DominionEng/CV-19_Guardian_Masks/Photos/(2).jpg

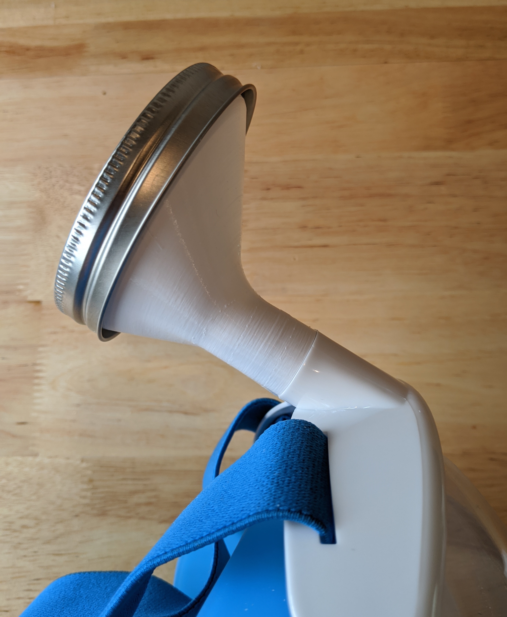
Photos/(2).jpg
