DominionEng/CV-19_Guardian_Masks/Photos/(3).jpg

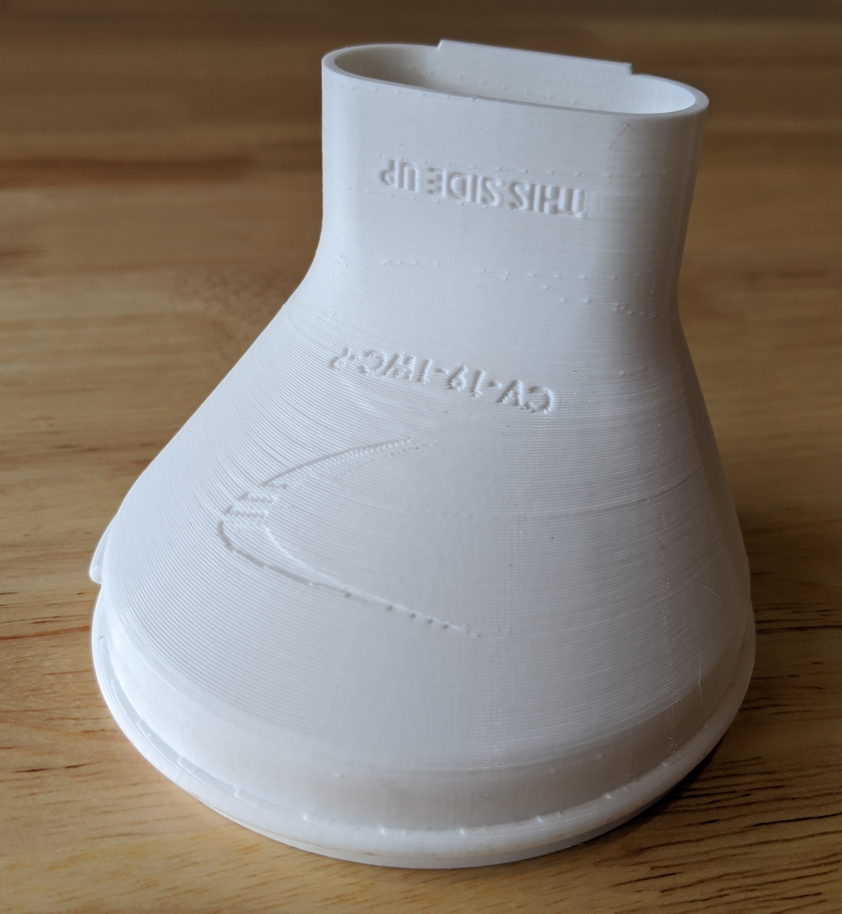
Photos/(3).jpg
