DominionEng/CV-19_Guardian_Masks/Photos/(4).jpg

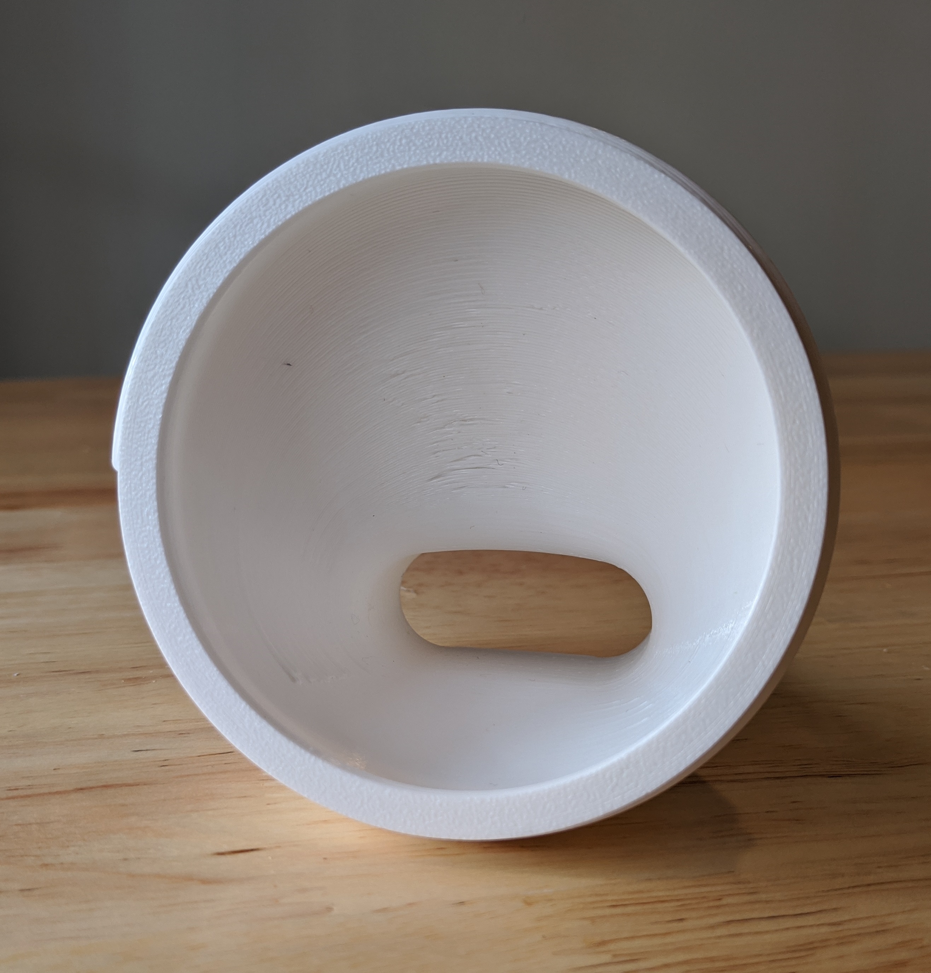
Photos/(4).jpg
