DominionEng/CV-19_Guardian_Masks/Photos/(6).JPG

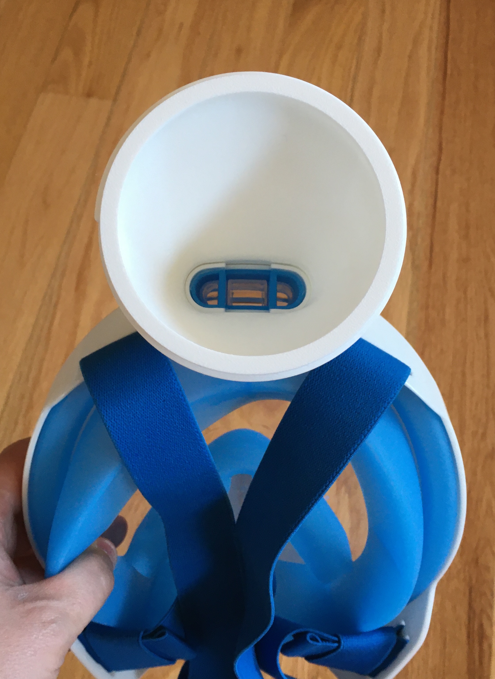
Photos/(6).JPG
