DominionEng/CV-19_Guardian_Masks/Photos/(7).JPG

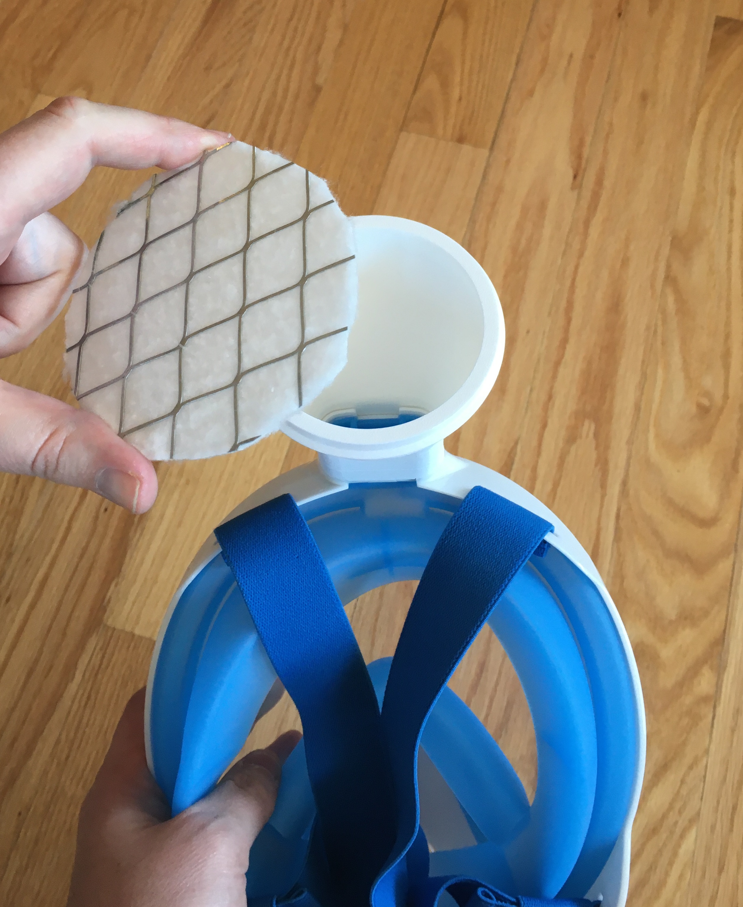
Photos/(7).JPG
