DominionEng/CV-19_Guardian_Masks/Photos/(9).jpg

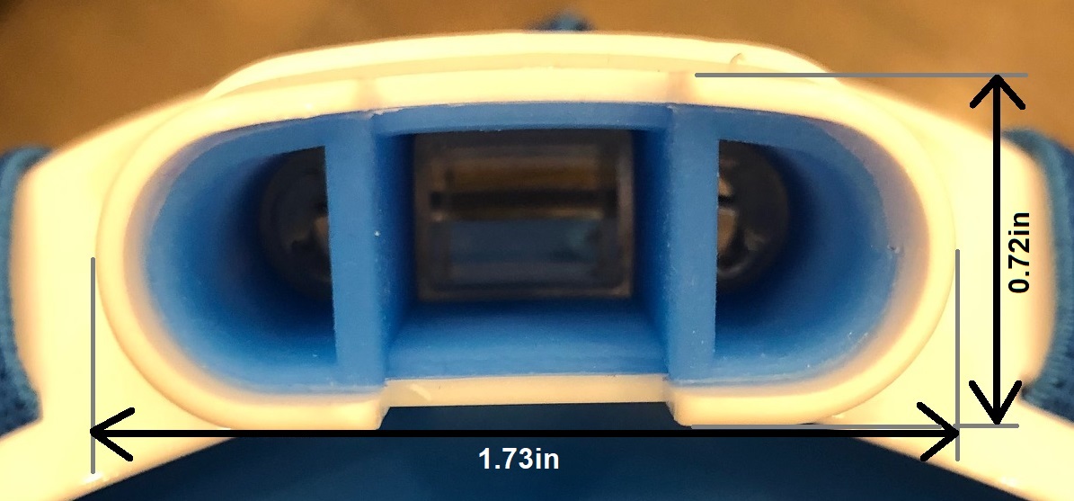
Photos/(9).jpg
