DominionEng/CV-19_Guardian_Masks/Photos/(10).jpg

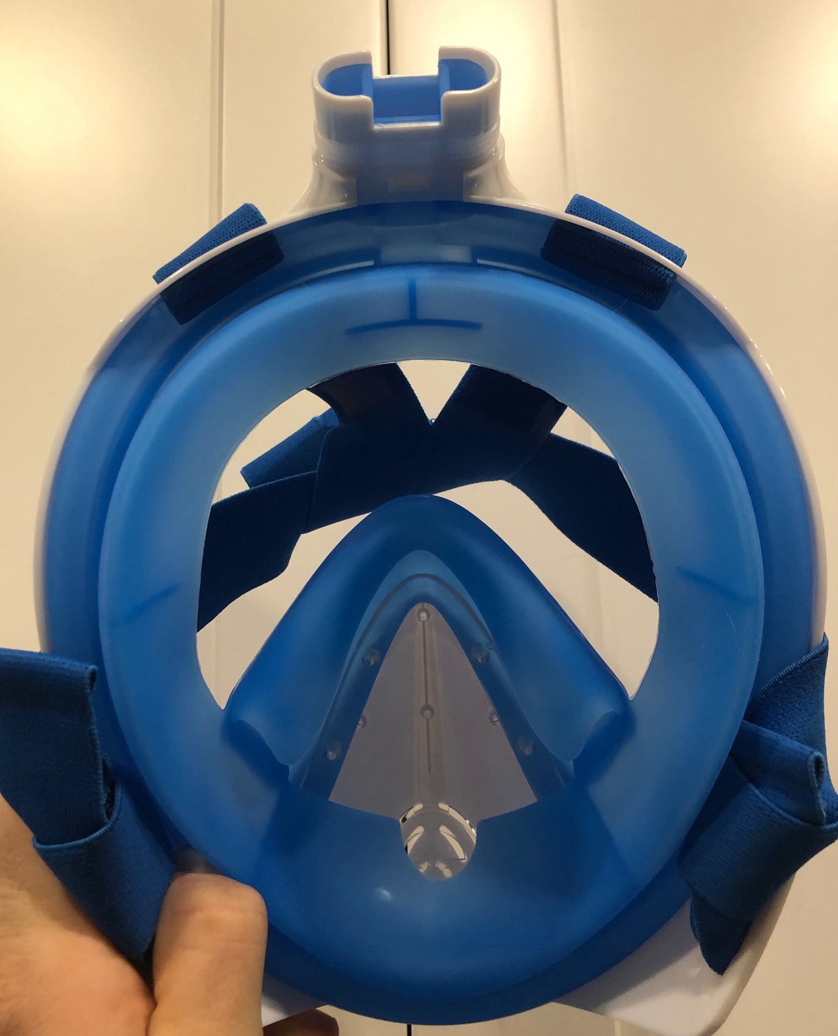
Photos/(10).jpg
