DominionEng/CV-19_Guardian_Masks/Photos/(11).JPG

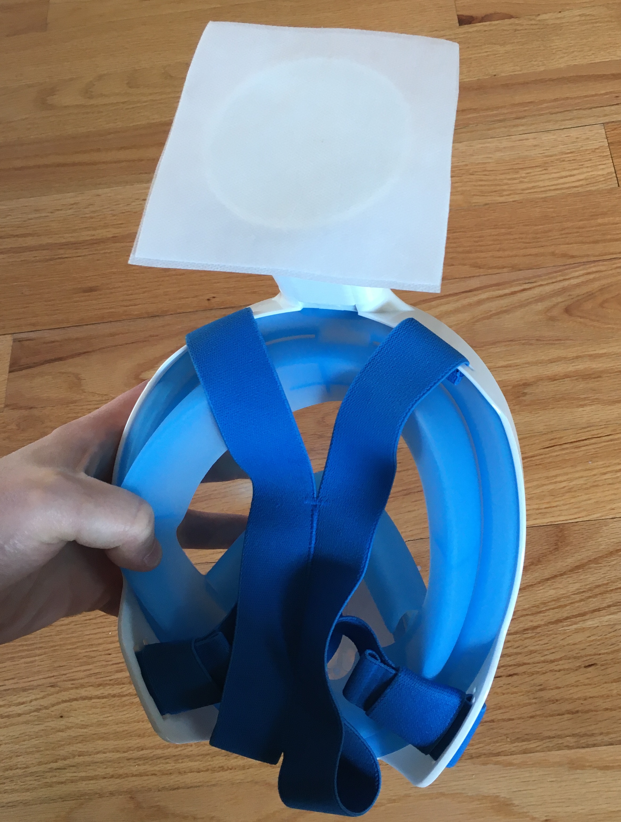
Photos/(11).JPG
