DominionEng/CV-19_Guardian_Masks/Photos/(12).JPG

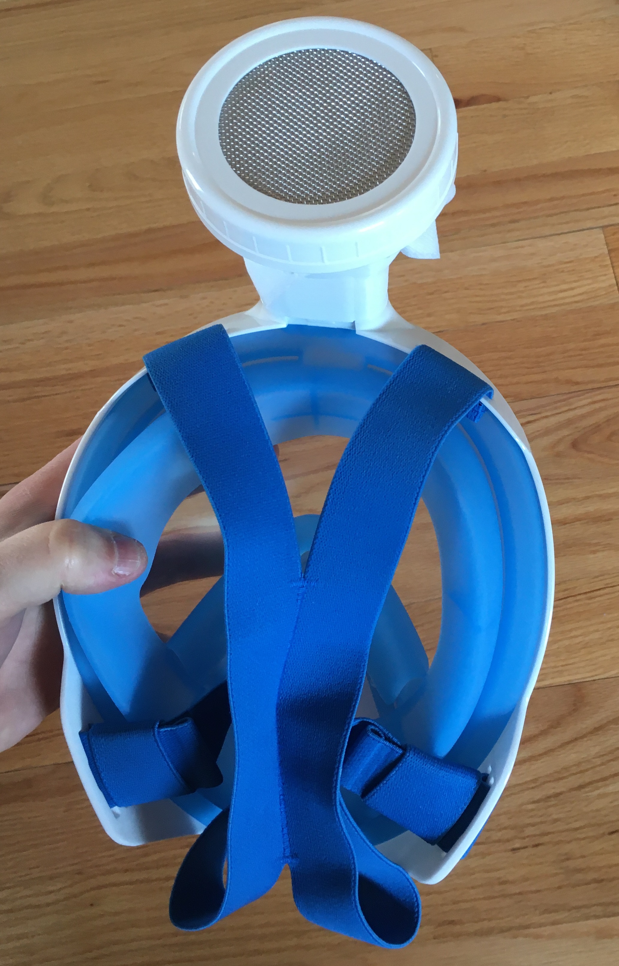
Photos/(12).JPG
